dbalsom/arduino808x/sketches/cpu_server/opcodes.h

/*
    Arduino8088 Copyright 2022-2025 Daniel Balsom
    https://github.com/dbalsom/arduino_8088

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
    THE SOFTWARE IS PROVIDED “AS IS”, WITHOUT WARRANTY OF ANY KIND, EXPRESS OR
    IMPLIED, INCLUDING BUT NOT LIMITED TO THE WARRANTIES OF MERCHANTABILITY,
    FITNESS FOR A PARTICULAR PURPOSE AND NONINFRINGEMENT. IN NO EVENT SHALL THE
    AUTHORS OR COPYRIGHT HOLDERS BE LIABLE FOR ANY CLAIM, DAMAGES OR OTHER   
    LIABILITY, WHETHER IN AN ACTION OF CONTRACT, TORT OR OTHERWISE, ARISING
    FROM, OUT OF OR IN CONNECTION WITH THE SOFTWARE OR THE USE OR OTHER
    DEALINGS IN THE SOFTWARE.
*/
#ifndef _ARDUINO8088_OPCODES_H
#define _ARDUINO8088_OPCODES_H

#define OPCODE_NOP 0x90
#define OPCODE_80NOP 0x00
#define OPCODE_DOUBLENOP 0x9090
#define OPCODE_DOUBLE_80NOP 0x0000

#define MODRM_OP(M) (((M & 0b00111000) >> 3) & 0x07)

#define GRP1 105
#define GRP2A 106
#define GRP2B 110
#define GRP3 107
#define GRP4 108
#define GRP5 109
#define IS_GRP_OP(O) ((OPCODE_REFS[O] >= GRP1) && (OPCODE_REFS[O] <= GRP2B))

// LUT of primary opcode to Mnemonic (Or Group name)
static const uint8_t OPCODE_REFS[] = {
  0, 0, 0, 0, 0, 0, 1, 2, 3, 3, 3, 3, 3, 3, 1, 2, 4, 4, 4, 4, 4, 4, 1, 2, 5, 5, 5, 5, 5, 5, 1, 2,
  6, 6, 6, 6, 6, 6, 7, 8, 9, 9, 9, 9, 9, 9, 10, 11, 12, 12, 12, 12, 12, 12, 13, 14, 15, 15, 15,
  15, 15, 15, 16, 17, 18, 18, 18, 18, 18, 18, 18, 18, 19, 19, 19, 19, 19, 19, 19, 19, 1, 1, 1, 1,
  1, 1, 1, 1, 2, 2, 2, 2, 2, 2, 2, 2, 20, 21, 22, 23, 24, 25, 26, 27, 28, 29, 30, 31, 32, 33, 34,
  35, 20, 21, 22, 23, 24, 25, 26, 27, 28, 29, 30, 31, 32, 33, 34, 35, 105, 105, 105, 105, 36, 36,
  37, 37, 38, 38, 38, 38, 38, 39, 38, 2, 111, 37, 37, 37, 37, 37, 37, 37, 40, 41, 42, 103, 43,
  44, 45, 46, 38, 38, 38, 38, 47, 48, 49, 50, 36, 36, 51, 52, 53, 54, 55, 56, 38, 38, 38, 38, 38,
  38, 38, 38, 38, 38, 38, 38, 38, 38, 38, 38, 57, 57, 57, 57, 58, 59, 38, 38, 60, 60, 60, 60, 61,
  61, 62, 63, 106, 106, 110, 110, 71, 73, 104, 75, 104, 104, 104, 104, 104, 104, 104, 104, 76,
  77, 78, 79, 80, 80, 81, 81, 82, 83, 84, 83, 80, 80, 81, 81, 85, 104, 86, 87, 89, 90, 107, 107,
  97, 98, 99, 100, 101, 102, 108, 109,
};

static const uint8_t OPCODE_8080_REFS[] = {
  0, 1, 2, 3, 4, 5, 6, 7, 80, 8, 9, 10, 4, 5, 6, 11, 80, 1, 2, 3, 4, 5, 6, 12, 80, 8, 9, 10, 4,
  5, 6, 13, 80, 1, 14, 3, 4, 5, 6, 15, 80, 8, 16, 10, 4, 5, 6, 17, 80, 1, 18, 3, 4, 5, 6, 19, 80,
  8, 20, 10, 4, 5, 6, 21, 22, 22, 22, 22, 22, 22, 22, 22, 22, 22, 22, 22, 22, 22, 22, 22, 22, 22,
  22, 22, 22, 22, 22, 22, 22, 22, 22, 22, 22, 22, 22, 22, 22, 22, 22, 22, 22, 22, 22, 22, 22, 22,
  22, 22, 22, 22, 22, 22, 22, 22, 22, 22, 22, 22, 23, 22, 22, 22, 22, 22, 22, 22, 22, 22, 24, 24,
  24, 24, 24, 24, 24, 24, 25, 25, 25, 25, 25, 25, 25, 25, 26, 26, 26, 26, 26, 26, 26, 26, 27, 27,
  27, 27, 27, 27, 27, 27, 28, 28, 28, 28, 28, 28, 28, 28, 29, 29, 29, 29, 29, 29, 29, 29, 30, 30,
  30, 30, 30, 30, 30, 30, 31, 31, 31, 31, 31, 31, 31, 31, 32, 33, 34, 35, 36, 37, 38, 39, 40, 41,
  42, 80, 43, 44, 45, 39, 46, 33, 47, 48, 49, 37, 50, 39, 51, 80, 52, 53, 54, 80, 55, 39, 56, 33,
  57, 58, 59, 37, 60, 39, 61, 62, 63, 64, 65, 81, 68, 39, 69, 33, 70, 71, 72, 37, 73, 39, 74, 75,
  76, 77, 78, 80, 79, 39,
};

static char *OPCODE_STRS[] = {
  "ADD",
  "PUSH",
  "POP",
  "OR",
  "ADC",
  "SBB",
  "AND",
  "ES",
  "DAA",
  "SUB",
  "CS",
  "DAS",
  "XOR",
  "SS",
  "AAA",
  "CMP",
  "DS",
  "AAS",
  "INC",
  "DEC",
  "JO",
  "JNO",
  "JB",
  "JNB",
  "JZ",
  "JNZ",
  "JBE",
  "JNBE",
  "JS",
  "JNS",
  "JP",
  "JNP",
  "JL",
  "JNL",
  "JLE",
  "JNLE",
  "TEST",
  "XCHG",
  "MOV",
  "LEA",
  "CBW",
  "CWD",
  "CALLF",
  "PUSHF",
  "POPF",
  "SAHF",
  "LAHF",
  "MOVSB",
  "MOVSW",
  "CMPSB",
  "CMPSW",
  "STOSB",
  "STOSW",
  "LODSB",
  "LODSW",
  "SCASB",
  "SCASW",
  "RETN",
  "LES",
  "LDS",
  "RETF",
  "INT",
  "INTO",
  "IRET",
  "ROL",
  "ROR",
  "RCL",
  "RCR",
  "SHL",
  "SHR",
  "SAR",
  "AAM",
  "AMX",
  "AAD",
  "ADX",
  "XLAT",
  "LOOPNE",
  "LOOPE",
  "LOOP",
  "JCXZ",
  "IN",
  "OUT",
  "CALL",
  "JMP",
  "JMPF",
  "LOCK",
  "REPNZ",
  "REP",
  "REPZ",
  "HLT",
  "CMC",
  "NOT",
  "NEG",
  "MUL",
  "IMUL",
  "DIV",
  "IDIV",
  "CLC",
  "STC",
  "CLI",
  "STI",
  "CLD",
  "STD",
  "WAIT",
  "INVAL",
  "GRP1",
  "GRP2A",
  "GRP3",
  "GRP4",
  "GRP5",
  "GRP2B",
  "NOP",
  
};

// 0x80 - 0x81
static char *OPCODE_STRS_GRP1[] = {
  "ADD",
  "OR",
  "ADC",
  "SBB",
  "AND",
  "SUB",
  "XOR",
  "CMP"
};

// 0xD0 - 0xD1
static char *OPCODE_STRS_GRP2A[] = {
  "ROL",
  "ROR",
  "RCL",
  "RCR",
  "SHL",
  "SHR",
  "SETMO",
  "SAR"
};

// 0xD2 - 0xD3
static char *OPCODE_STRS_GRP2B[] = {
  "ROL",
  "ROR",
  "RCL",
  "RCR",
  "SHL",
  "SHR",
  "SETMOC",
  "SAR"
};

// 0xF6 - 0xF7
static char *OPCODE_STRS_GRP3[] = {
  "TEST",
  "TEST",
  "NOT",
  "NEG",
  "MUL",
  "IMUL",
  "DIV",
  "IDIV",
};

// 0xFE
static char *OPCODE_STRS_GRP4[] = {
  "INC",
  "DEC",
  "INVAL",
  "INVAL",
  "INVAL",
  "INVAL",
  "INVAL",
  "INVAL"
};

// 0xFF
static char *OPCODE_STRS_GRP5[] = {
  "INC",
  "DEC",
  "CALL",
  "CALLF",
  "JMP",
  "JMPF",
  "PUSH",
  "INVAL"
};

static char *OPCODE_8080_STRS[] = {
  "NOP",
  "LXI",
  "STAX",
  "INX",
  "INR",
  "DCR",
  "MVI",
  "RLC",
  "DAD",
  "LDAX",
  "DCX",
  "RRC",
  "RAL",
  "RAR",
  "SHLD",
  "DAA",
  "LHLD",
  "CMA",
  "STA",
  "STC",
  "LDA",
  "CMC",
  "MOV",
  "HLT",
  "ADD",
  "ADC",
  "SUB",
  "SBB",
  "ANA",
  "XRA",
  "ORA",
  "CMP",
  "RNZ",
  "POP",
  "JNZ",
  "JMP",
  "CNZ",
  "PUSH",
  "ADI",
  "RST",
  "RZ",
  "RET",
  "JZ",
  "CZ",
  "CALL",
  "ACI",
  "RNC",
  "JNC",
  "OUT",
  "CNC",
  "SUI",
  "RC",
  "JC",
  "IN",
  "CC",
  "SBI",
  "RPO",
  "JPO",
  "XTHL",
  "CPO",
  "ANI",
  "RPE",
  "PCHL",
  "JPE",
  "XCHG",
  "CPE",
  "CALLN",
  "RETEM",
  "XRI",
  "RP",
  "JP",
  "DI",
  "CP",
  "ORI",
  "RM",
  "SPHL",
  "JM",
  "EI",
  "CM",
  "CPI",
  "INVAL",
  "EXT",
};

#endif 
